ytmytm/1541-RAMBOardII/doc/dsc_0012-2.webp

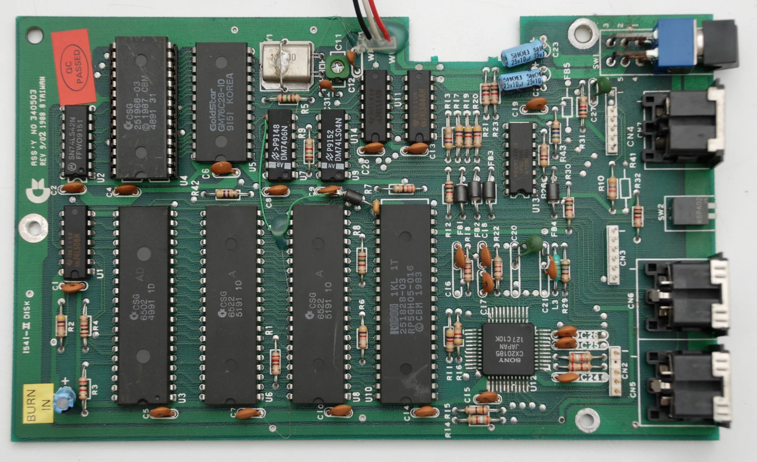
doc/dsc_0012-2.webp
