ytmytm/1541-RAMBOardII/doc/dsc_0013-1.webp

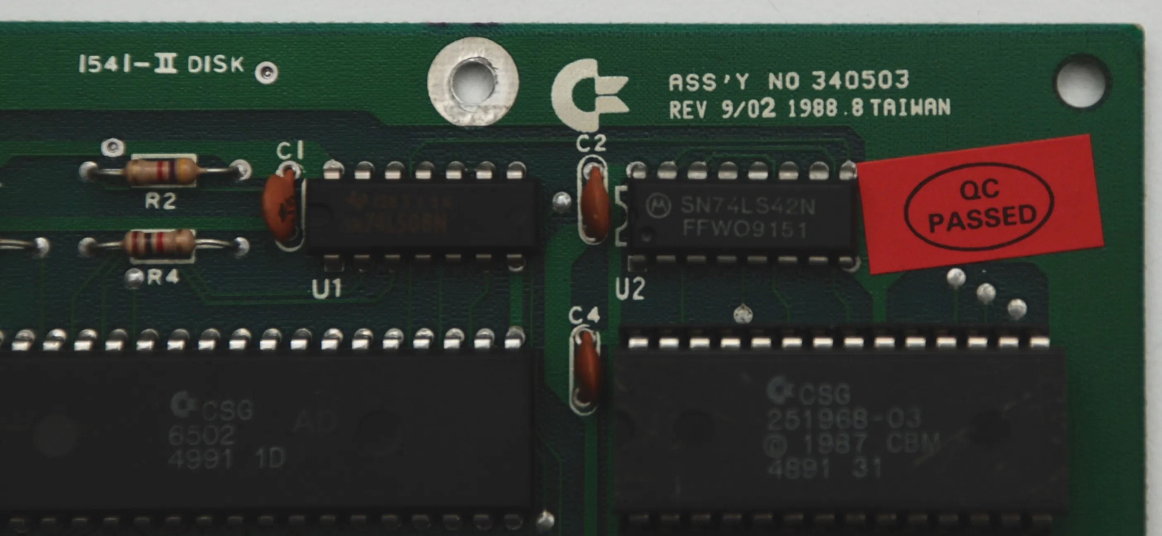
doc/dsc_0013-1.webp
